MonzurulAlam/OpenXamp/3amp_BioAmp/Simulations/3ampIA.asc

C1: cap; 1nF
C2: cap; 4.7µ
R1: res; 5.49K
R2: res; 62K; tol=1 pwr=0.1
R3: res; 10K
R4: res; 100K; tol=1 pwr=0.1
R5: res; 100K
U1: AD8220
U2: OP2177
U3: OP2177
V1: voltage; 3.7
V2: voltage; -3.7
V3: voltage; 200m
Vcm: voltage; 500m
Vin: voltage; SINE(0 5m 100)
Named nets: +V, 0, Out1, -V, Out2, Out3
.tran 1 uic
